lnis-uofu/MemoryCharacterizationSystem/chip_cadence_files/cmi_4mm_template/dicing_cross/layout/thumbnail_128x128.png

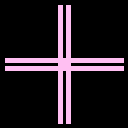
chip_cadence_files/cmi_4mm_template/dicing_cross/layout/thumbnail_128x128.png
