lnis-uofu/MemoryCharacterizationSystem/chip_cadence_files/reram_library_rev4/pad_angle_top_left/layout/thumbnail_128x128.png

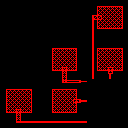
chip_cadence_files/reram_library_rev4/pad_angle_top_left/layout/thumbnail_128x128.png
