lnis-uofu/MemoryCharacterizationSystem/chip_cadence_files/reram_library_rev4/reram_chip_high_res.png

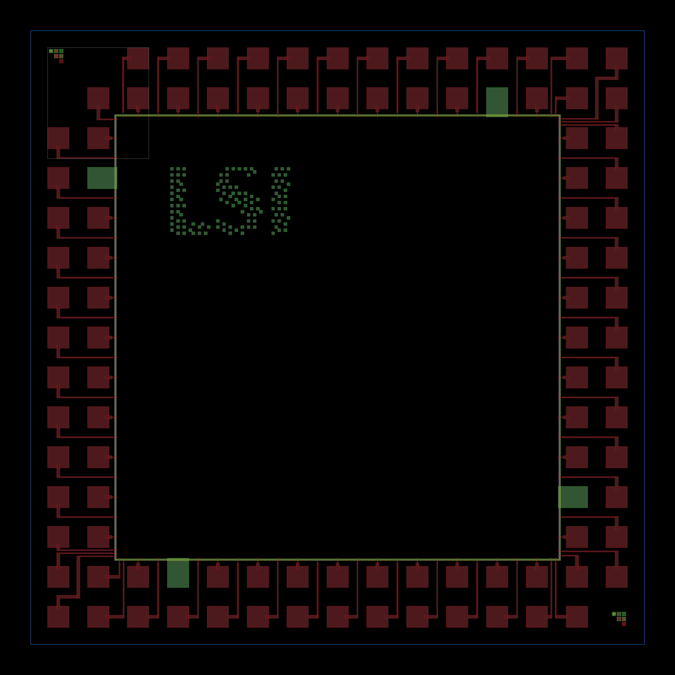
chip_cadence_files/reram_library_rev4/reram_chip_high_res.png
