lnis-uofu/MemoryCharacterizationSystem/chip_cadence_files/reram_library_rev4/reram_wafer_low_res.png

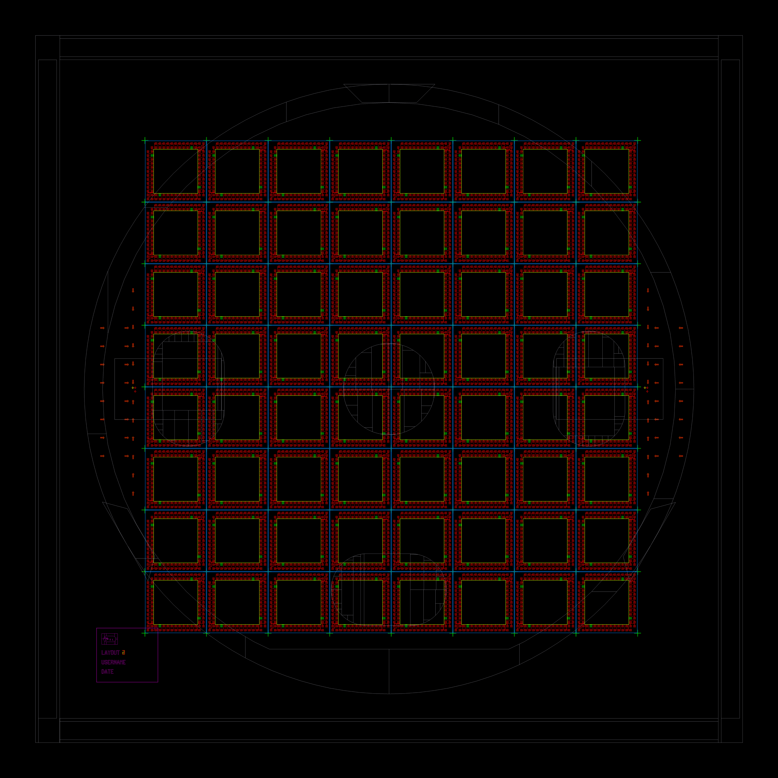
chip_cadence_files/reram_library_rev4/reram_wafer_low_res.png
