lnis-uofu/MemoryCharacterizationSystem/chip_cadence_files/reram_library_rev4/wafer/layout/thumbnail_128x128.png

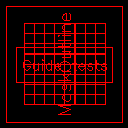
chip_cadence_files/reram_library_rev4/wafer/layout/thumbnail_128x128.png
